jzalewski94/arduino-sec-sys/models+3d-files/photos/20231221-DSC_1754.jpg

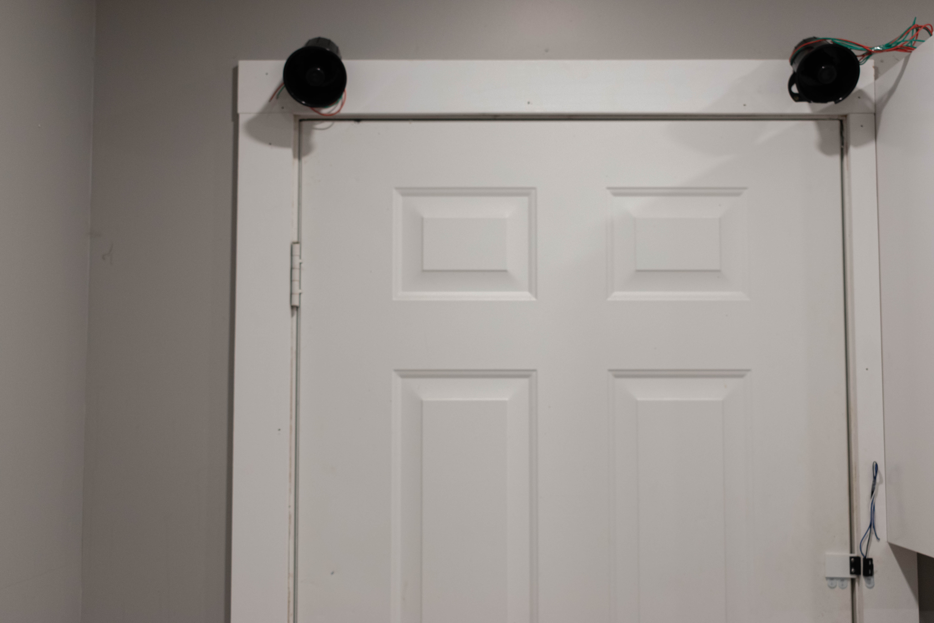
models+3d-files/photos/20231221-DSC_1754.jpg
