jzalewski94/arduino-sec-sys/models+3d-files/photos/20240102-DSC_1846.jpg

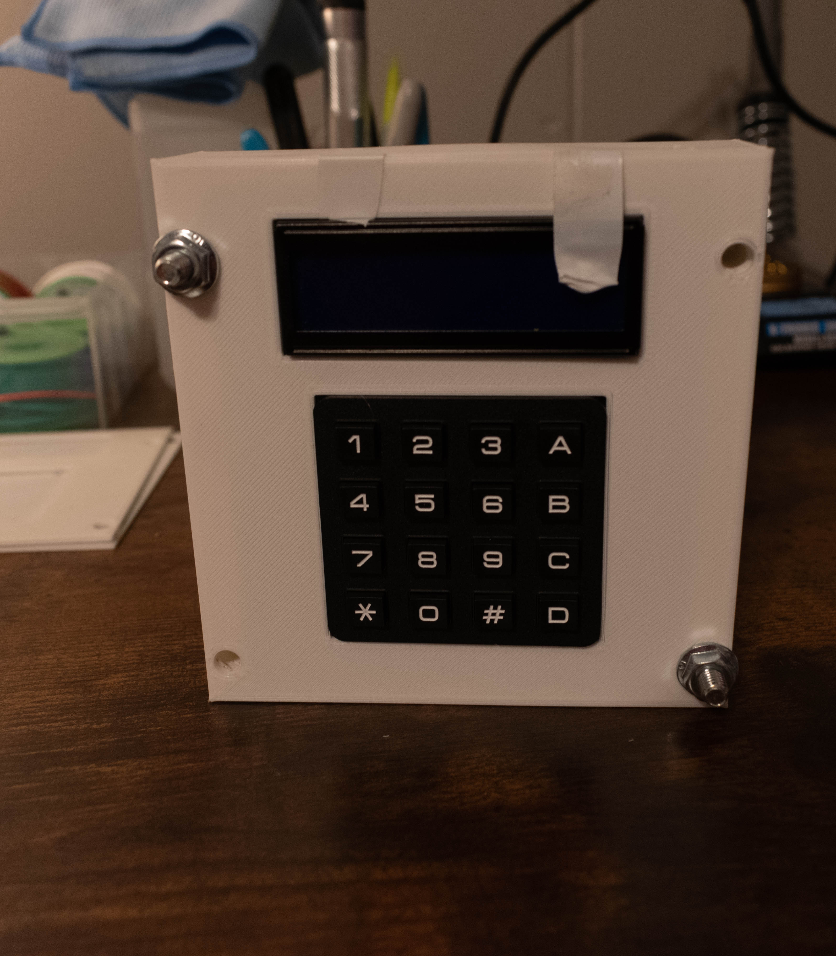
models+3d-files/photos/20240102-DSC_1846.jpg
